MadsRudolph/34621-Metal-Detector/Literature/20240103_144208.jpg

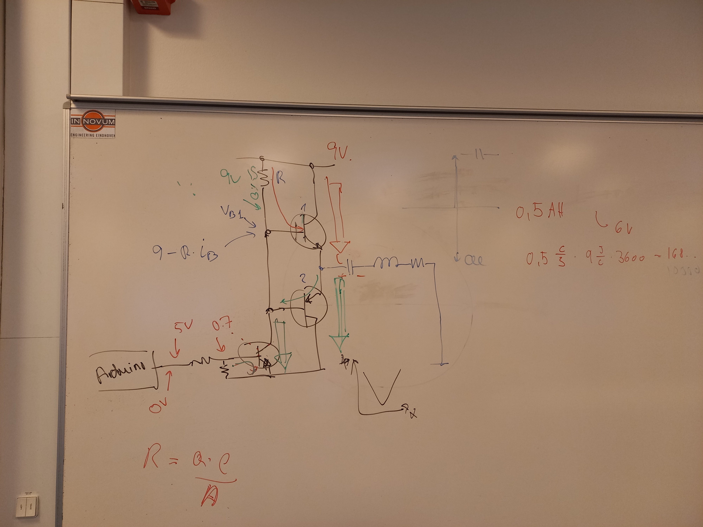
Literature/20240103_144208.jpg
