MadsRudolph/34621-Metal-Detector/Docs/Templates/Circuit Note.md

# {{Circuit Name}}

**Type:** (Amplifier / Filter / Driver / Power Supply)  
**Status:** ⬜ Design | ⬜ Simulated | ⬜ Built | ⬜ Tested

---

## Purpose

## Schematic

![[{{schematic_image}}]]

## Component Values

| Component | Value | Part Number | Notes |
|---|---|---|---|
| R1 | | | |
| C1 | | | |
| U1 | | | |

## Design Calculations

### Input Parameters
- 

### Calculations
$$

$$

### Expected Output
- 

## Simulation Results

**LTspice File:** [[LTspice/simulations/{{filename}}.asc]]

### Transient Analysis

### AC Analysis (Bode Plot)

## Test Results

| Parameter | Expected | Measured | Pass? |
|---|---|---|---|
| | | | |

## Issues & Solutions

## Related
- [[KiCad/README|KiCad Schematic]]
- [[LTspice/README|LTspice Simulation]]

---
#circuit #analog
