MadsRudolph/34621-Metal-Detector/Docs/Meetings/Referat af møde 8-1-2026.md

Vi har lavet et spole design tunening kan forekomme
Vi har gennemført simulering af forskellige varianter af spole dimensioner
Softwaren for TX, RX og DSP delen er ved at være nået til et punkt hvor det kan testes
Vi har lavet en fungerende Hbro forstærker til A.P forstærkeren, der er enkelte problemer bla at PMOS'erne i kredsløbet måske ville ryge ud af saturation lidt efter lidt som batteriet taber spænding.
Vi har sat os fast på en spole ydre diameter på 20cm så vi kan gå i gang med at lave en 3D model af metaldetektoren.
Vi ville gerne have en prototype udgave af softwaren både til DSP, Tx, Rx og A.P styring klar til slutningen af den 9-1-2026.
Til uge 3 skal alt være klar til test så vi kan udnytte ugen til test og redesign.
Rx forstærkeren skal have et færdigt grunddesign til begyndelsen af uge 3, så vi kan teste justeringer kan forekomme.
Vi ville gerne så småt begynde at skrive vores sota og analyse ind i raporten fra idag af.
