MadsRudolph/34621-Metal-Detector/Docs/Templates/Daily Note.md

# {{date:YYYY-MM-DD}} - Daily Log

## 🎯 Goals for Today
- [ ] 
- [ ] 
- [ ] 

## ✅ Completed
- 

## 📝 Notes

## ❓ Questions
- 

## 🐛 Issues Encountered

## 📅 Tomorrow
- 

---
#daily
