MadsRudolph/34621-Metal-Detector/Docs/Templates/Literature Note.md

# {{title}}

**Source:** [[Literature/{{filename}}]]  
**Date Read:** {{date}}  
**Relevance:** ⭐⭐⭐⭐⭐

---

## Summary

## Key Concepts

### Concept 1

### Concept 2

## Important Equations

$$

$$

## Figures/Diagrams

## How This Applies to Our Project

## Questions

## Related Notes
- 

---
#literature #reading-notes
