MadsRudolph/34621-Metal-Detector/assets/photos/3D_modeller_samlet.png

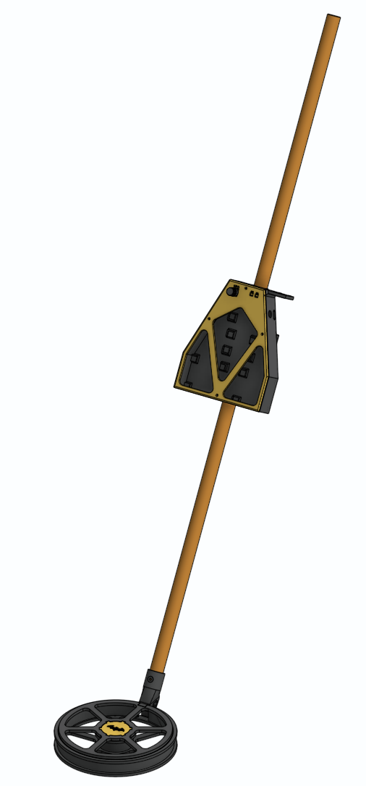
assets/photos/3D_modeller_samlet.png
