MadsRudolph/34621-Metal-Detector/assets/photos/Dead_Time_forklarings_diagram.png

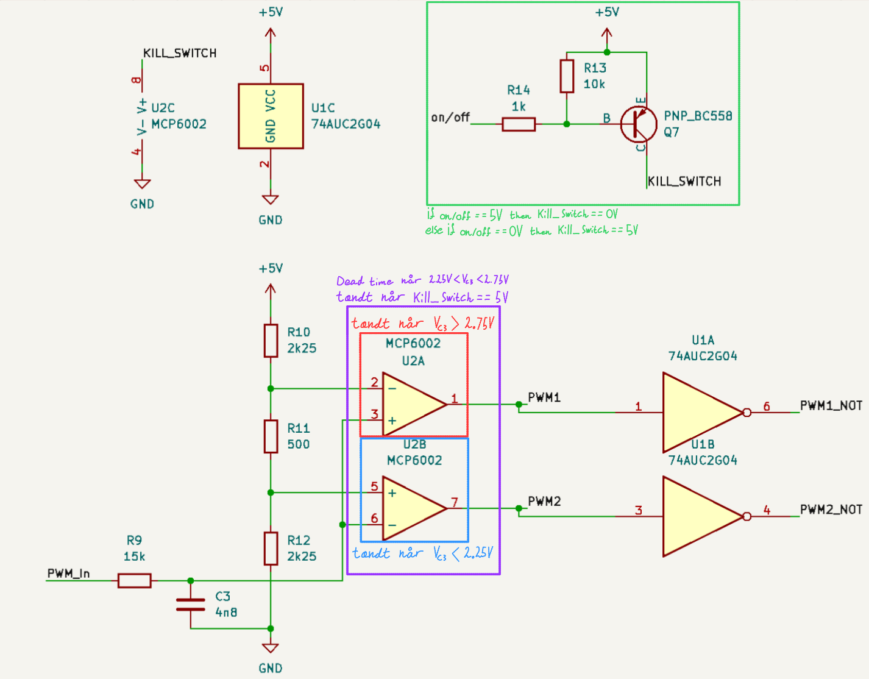
assets/photos/Dead_Time_forklarings_diagram.png
