MadsRudolph/34621-Metal-Detector/assets/photos/Dead_Time_PCB.png

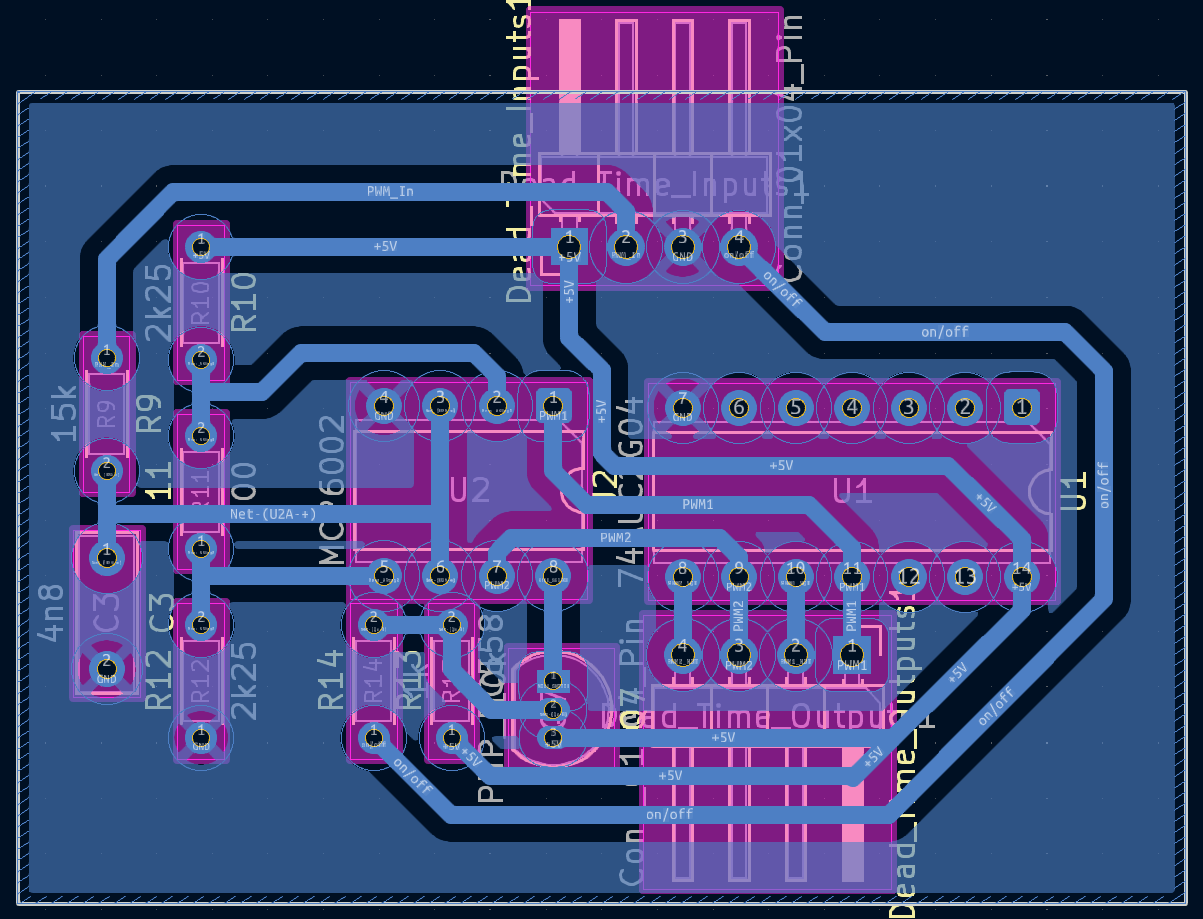
assets/photos/Dead_Time_PCB.png
