MadsRudolph/34621-Metal-Detector/assets/photos/Højre_PCB.png

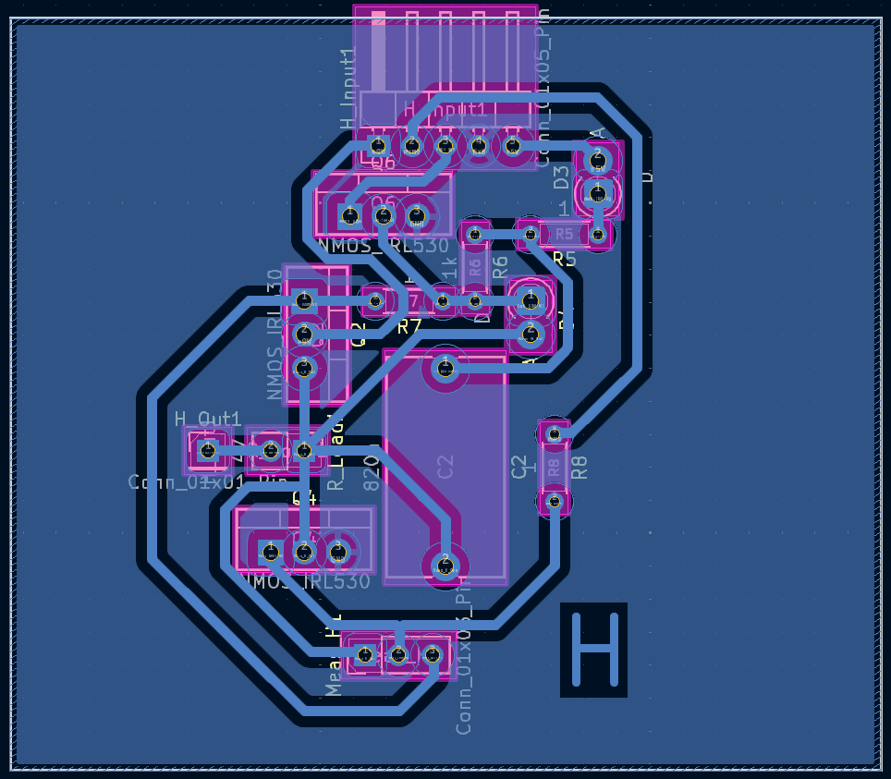
assets/photos/Højre_PCB.png
