MadsRudolph/34621-Metal-Detector/assets/photos/RX-filter_simulation.png

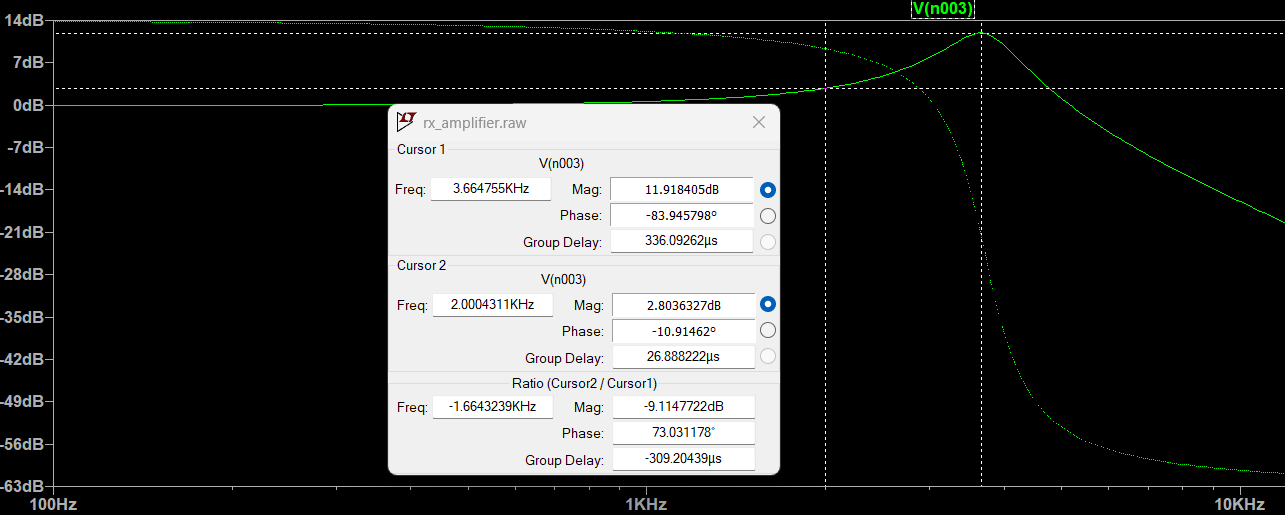
assets/photos/RX-filter_simulation.png
