MadsRudolph/34621-Metal-Detector/assets/photos/Rx_amp.png

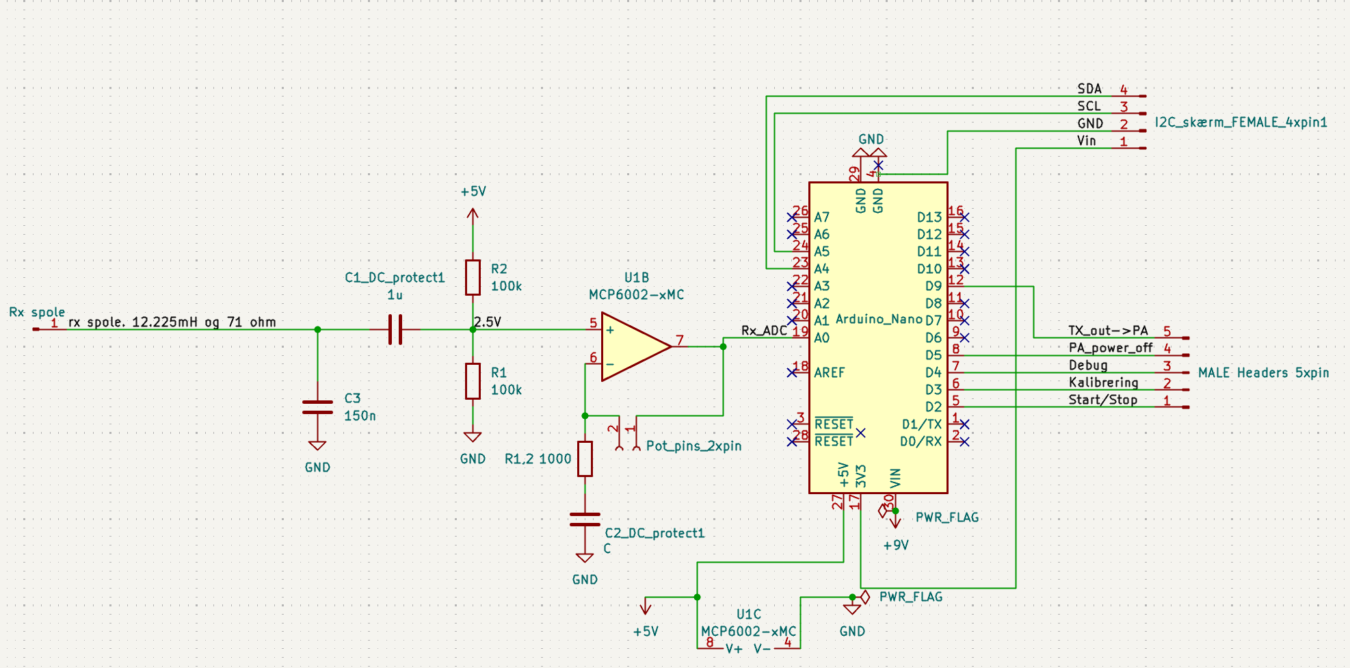
assets/photos/Rx_amp.png
