MadsRudolph/34621-Metal-Detector/assets/photos/Rx_forstærker_PCB.png

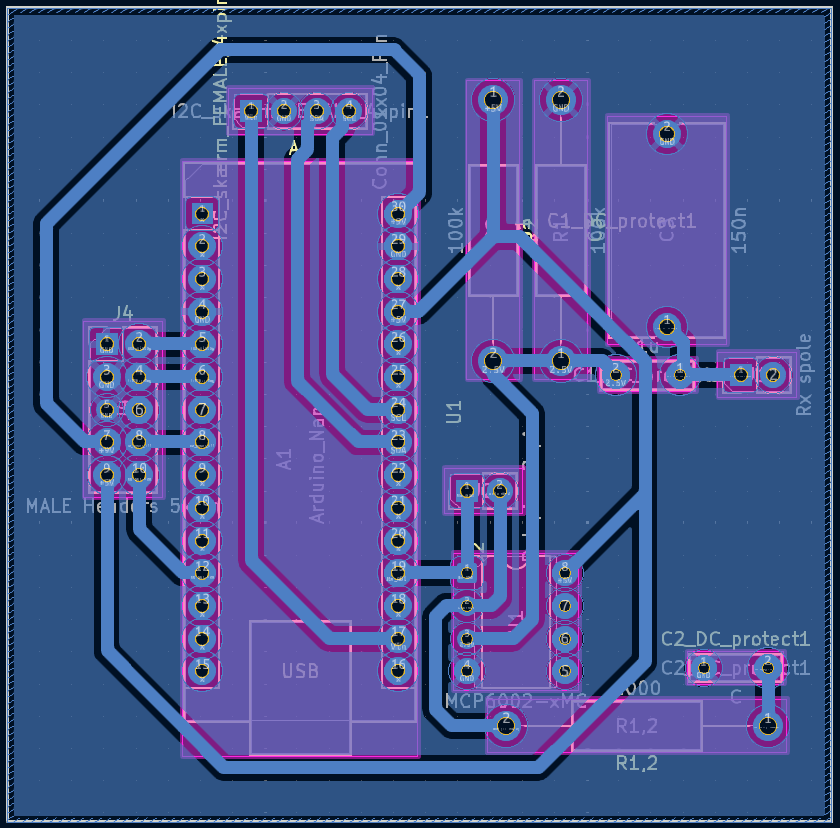
assets/photos/Rx_forstærker_PCB.png
