MadsRudolph/34621-Metal-Detector/assets/photos/Simulering_Hbro.png

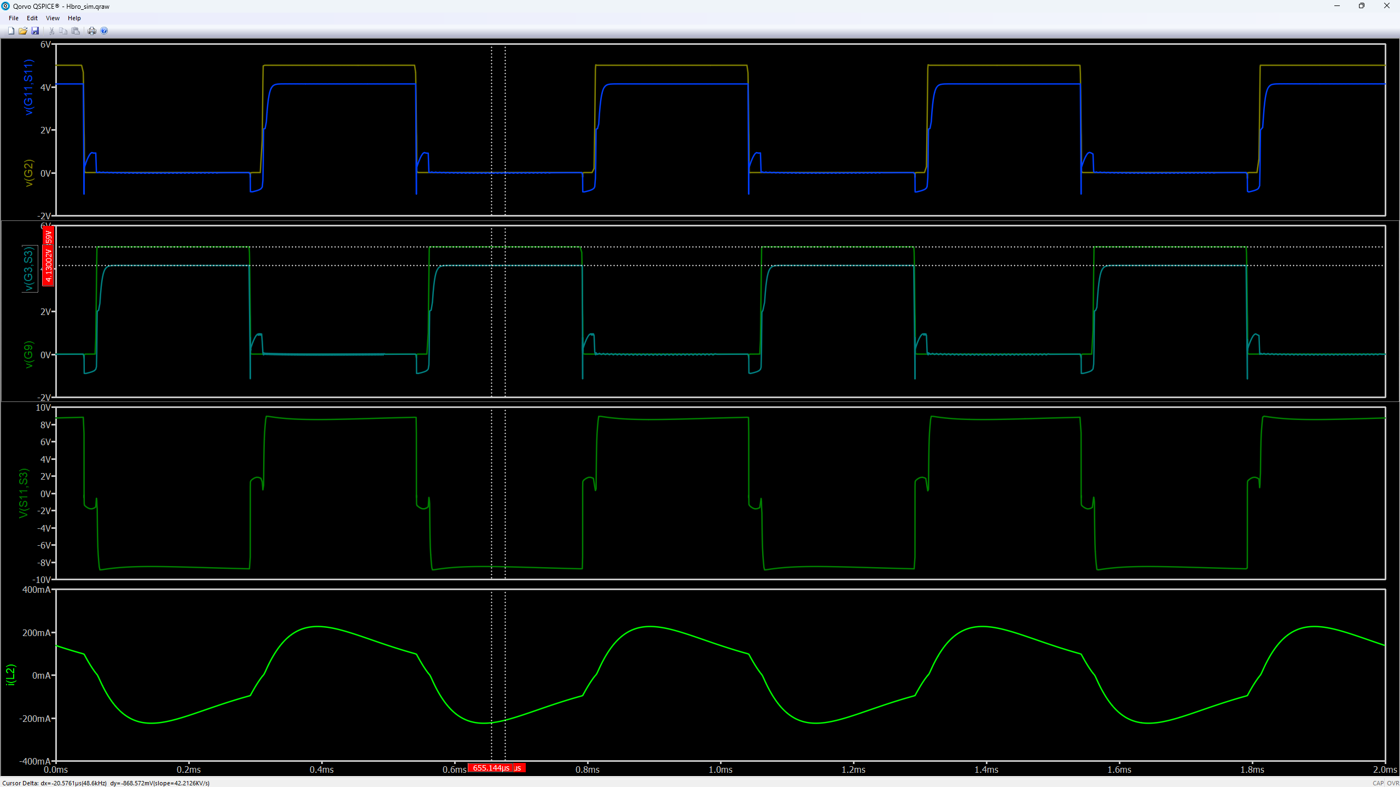
assets/photos/Simulering_Hbro.png
