MadsRudolph/34621-Metal-Detector/assets/photos/Timer1.png

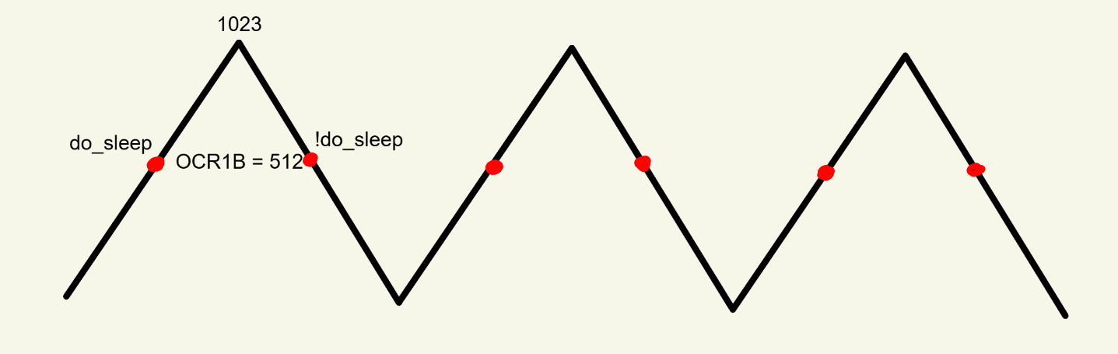
assets/photos/Timer1.png
