MadsRudolph/34621-Metal-Detector/Docs/Images/Deadtime_Blue-PWM1_not_Yellow-PWM1___5_us.png

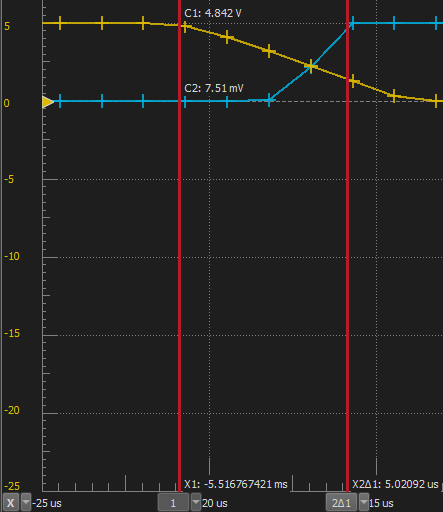
Docs/Images/Deadtime_Blue-PWM1_not_Yellow-PWM1___5_us.png
