MadsRudolph/34621-Metal-Detector/Docs/Images/dft_samples.png

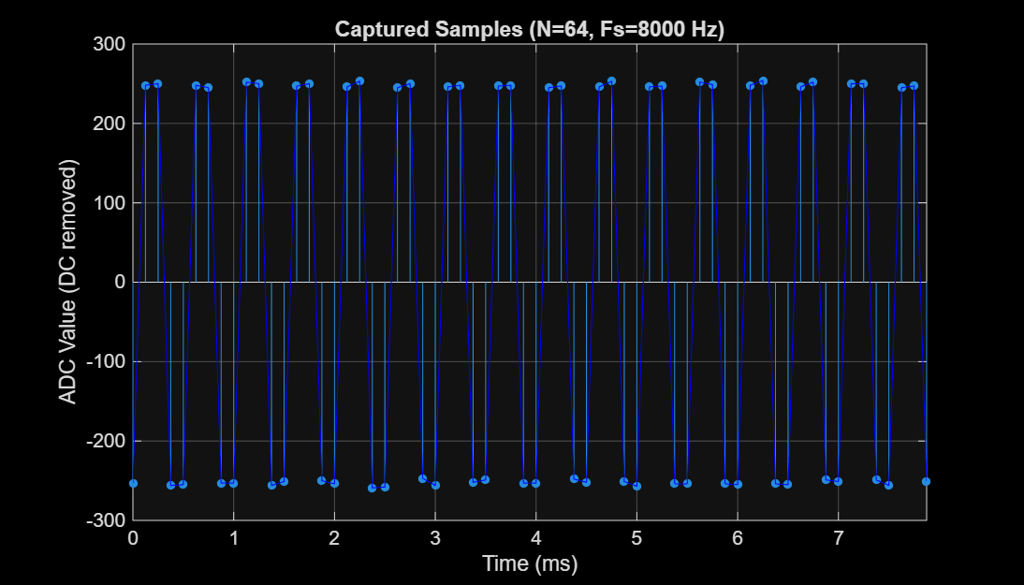
Docs/Images/dft_samples.png
