MadsRudolph/34621-Metal-Detector/Docs/Images/Differential_output.png

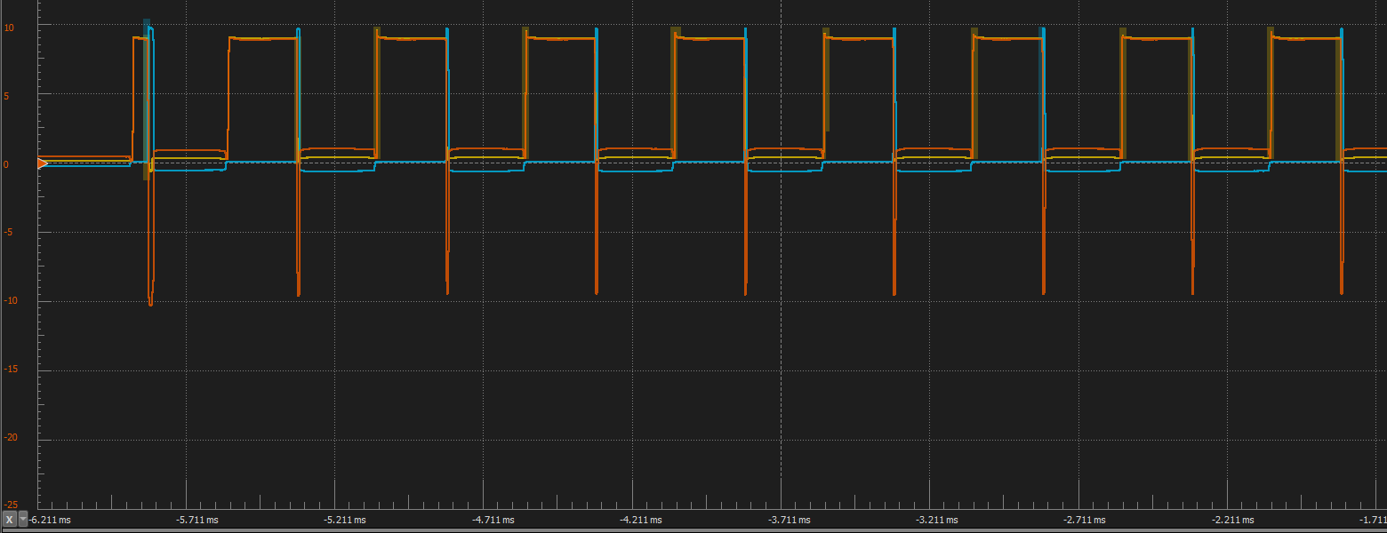
Docs/Images/Differential_output.png
