MadsRudolph/34621-Metal-Detector/Docs/Images/Gate_drive_signal_left_Yellow-Highside_Blue-lowside.png

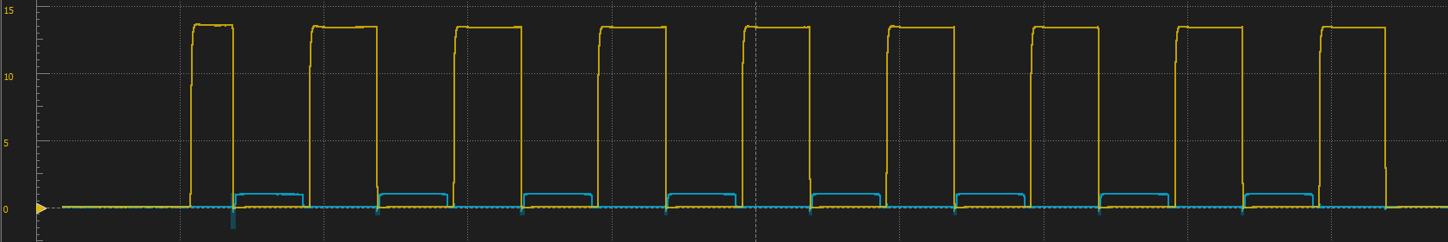
Docs/Images/Gate_drive_signal_left_Yellow-Highside_Blue-lowside.png
