MadsRudolph/34621-Metal-Detector/Docs/Images/Gates/gatem4_yellow-højre_blue-left.png

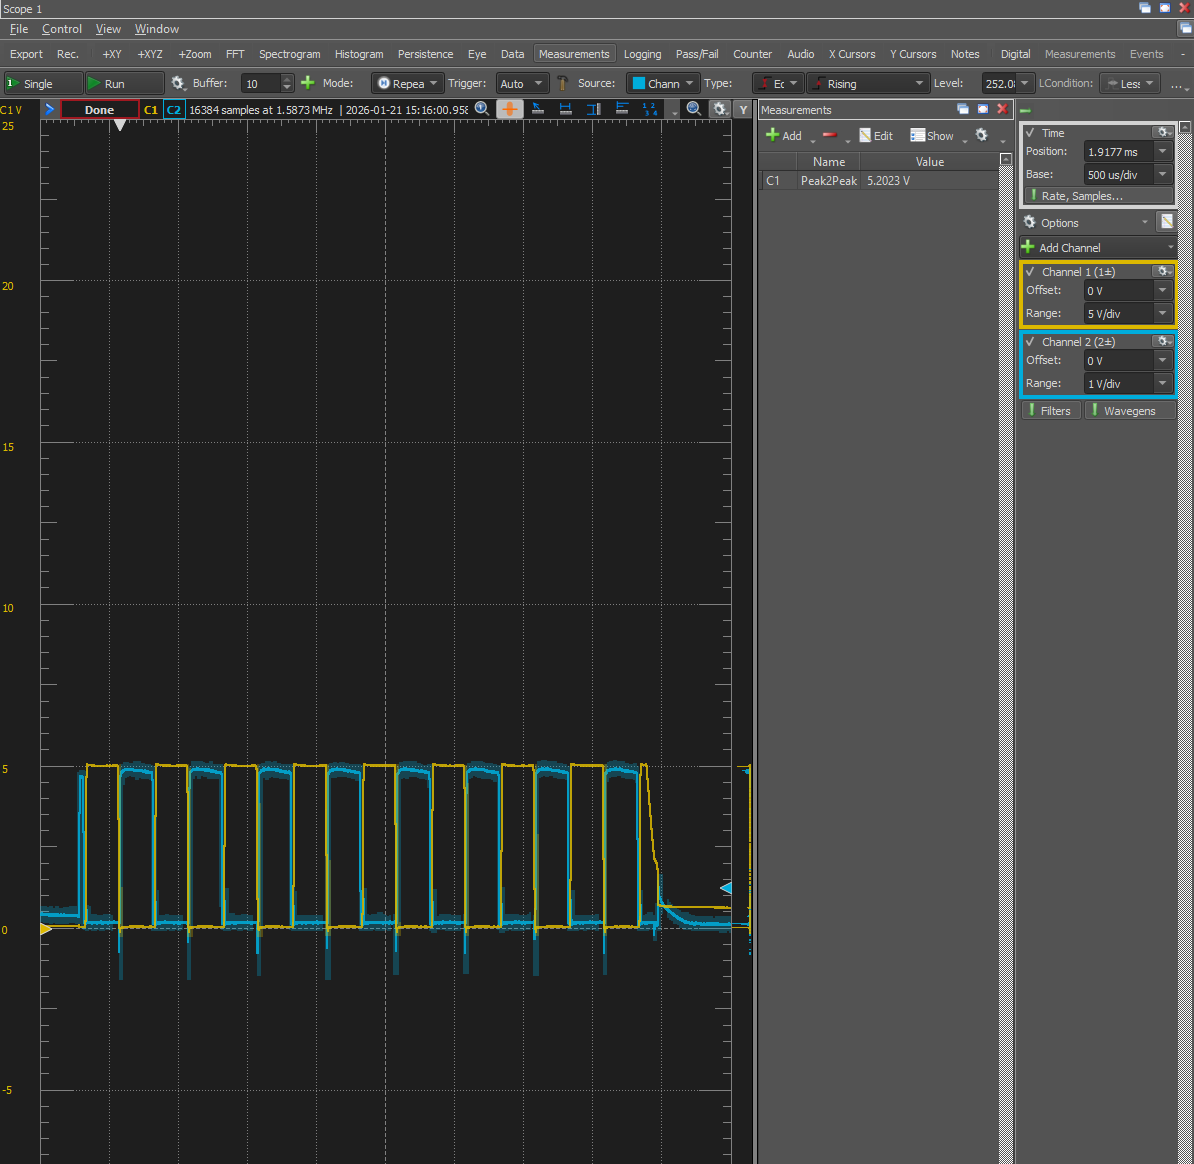
Docs/Images/Gates/gatem4_yellow-højre_blue-left.png
