MadsRudolph/34621-Metal-Detector/Docs/Images/Gates/gatem4_yellow-højre_blue-left_closeup.png

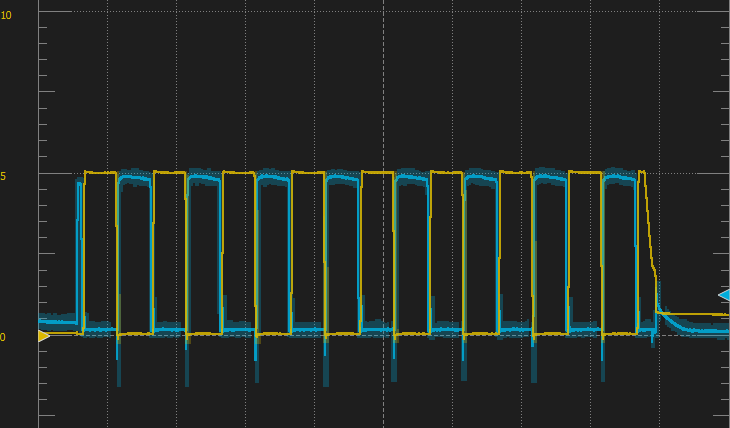
Docs/Images/Gates/gatem4_yellow-højre_blue-left_closeup.png
