MadsRudolph/34621-Metal-Detector/Docs/Images/nano_vs_mega.png

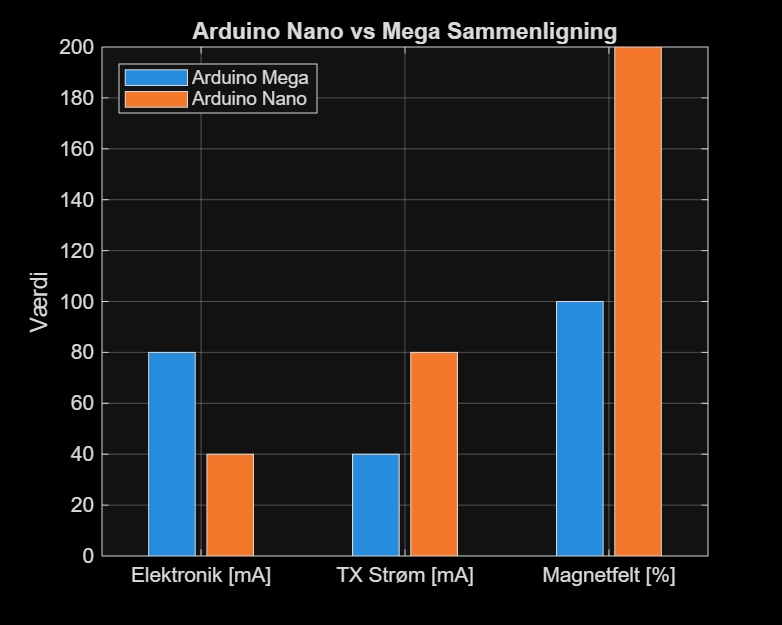
Docs/Images/nano_vs_mega.png
