MadsRudolph/34621-Metal-Detector/Docs/Images/tx_turns_vs_inductance.png

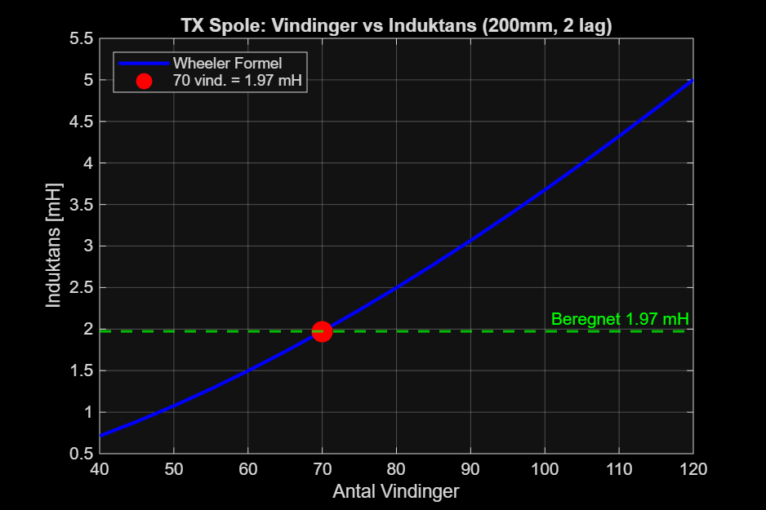
Docs/Images/tx_turns_vs_inductance.png
