MadsRudolph/34621-Metal-Detector/assets/photos/battery_discharge_test.png

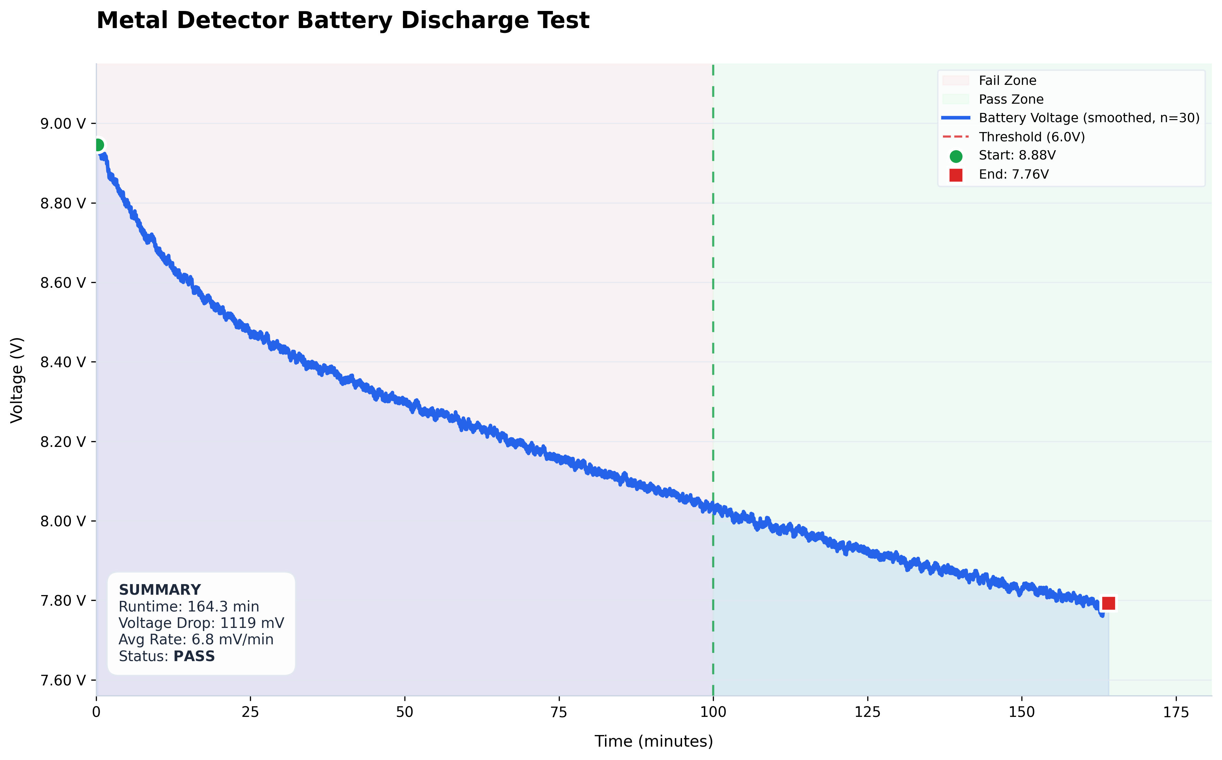
assets/photos/battery_discharge_test.png
