MadsRudolph/34621-Metal-Detector/Docs/Matlab/dft_verification.png

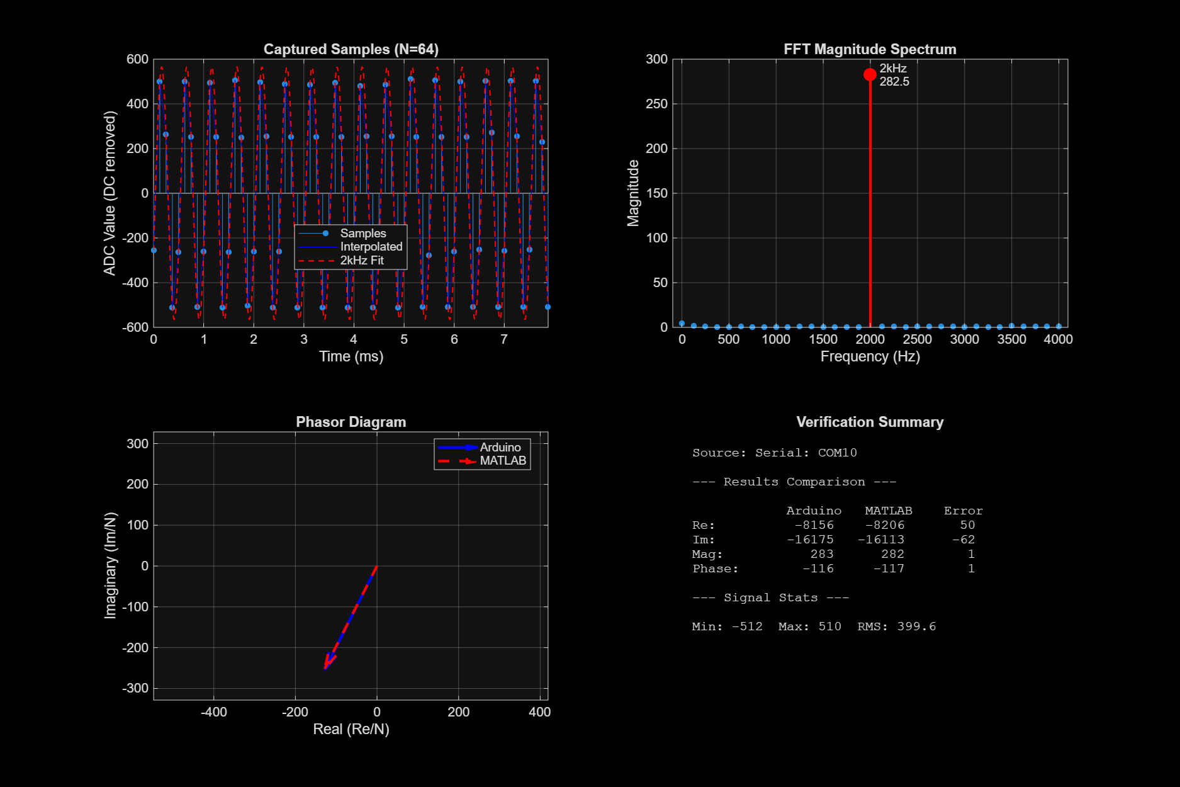
Docs/Matlab/dft_verification.png
