MadsRudolph/34621-Metal-Detector/LTspice/rx_amplifier.asc

C1: cap; 1µ
C2: cap; 1µ
C3: cap; 150n
L_rx_spole: ind; 12.255m
R1: res; 100k
R2: res; 100k
R3: res; 90k
R4: res; 14k
R_spole: res; 71
U1: UniversalOpAmp; Avol=1Meg GBW=1Meg Vos=0; En=0 Enk=0 In=0 Ink=0 Rin=1Meg
V1: voltage; 5
V2: voltage; SINE(0 200m 2k); AC 1
Named nets: 0
2.5V
.ac dec 100 1 1G
;.tran 50m
spole og modstand er en model af Rx spolens modstand og selvinduktans
