MadsRudolph/34621-Metal-Detector/LTspice/example.asc

C1: cap; 3µ
L1: ind; 0.00227
Q1: npn; BC337-25
Q2: npn; BC817-25
Q3: pnp; BC327-25
R1: res; 13.8
R2: res; 1k
R3: res; 10k
R4: res; 10k
V1: voltage; 9; Rser=1
V2: voltage; PULSE(0 5 0 1u 1u 0.25m 0.5m)
Named nets: 0
.tran 10ms
