MadsRudolph/34621-Metal-Detector/Code/src/drivers/data.h

/**
 * data.h
 * Font data for SSD1306 OLED display
 *
 * This file contains all the static arrays to draw things in the display.
 * You can create your own fonts using this tool: https://www.mikroe.com/glcd-font-creator
 *
 * ATTRIBUTION:
 * ============
 * Part of the SSD1306 driver by osch
 *
 * Integration: Mads Rudolph, Andreas Skaaning, Jonas Beck & Sigurd Hestbech (DTU 34621 Metal Detector Project)
 */

#ifndef DATA_H_
#define DATA_H_

#include <avr/pgmspace.h>
#include <stdint.h>

typedef uint8_t bitmap_t[8][128];
typedef char PROGMEM prog_uchar;

// Big numbers font, from 0 to 9. 96 byte each.
const prog_uchar bigNumbers [][96] PROGMEM = {
{0x00, 0x00, 0x00, 0xC0, 0xE0, 0xF0, 0xF0, 0xF0, 0xF0, 0xF0, 0xF0, 0xF0, 0xF0, 0xF0, 0xF0, 0xF0,
0xF0, 0xF0, 0xF0, 0xE0, 0xC0, 0x00, 0x00, 0x00, 0x00, 0x00, 0x00, 0xFF, 0xFF, 0xFF, 0xFF, 0x01,
0x00, 0x00, 0x00, 0x00, 0x00, 0x00, 0x00, 0x00, 0x01, 0xFF, 0xFF, 0xFF, 0xFF, 0x00, 0x00, 0x00,
0x00, 0x00, 0x00, 0xFF, 0xFF, 0xFF, 0xFF, 0x80, 0x00, 0x00, 0x00, 0x00, 0x00, 0x00, 0x00, 0x00,
0x80, 0xFF, 0xFF, 0xFF, 0xFF, 0x00, 0x00, 0x00, 0x00, 0x00, 0x00, 0x03, 0x07, 0x0F, 0x0F, 0x0F,
0x0F, 0x0F, 0x0F, 0x0F, 0x0F, 0x0F, 0x0F, 0x0F, 0x0F, 0x0F, 0x0F, 0x07, 0x03, 0x00, 0x00, 0x00},

{0x00, 0x00, 0x00, 0x00, 0x00, 0x00, 0x00, 0x00, 0x00, 0x00, 0x00, 0x00, 0x00, 0x00, 0xE0, 0xF0,
0xF0, 0xE0, 0x00, 0x00, 0x00, 0x00, 0x00, 0x00, 0x00, 0x00, 0x00, 0x00, 0x00, 0x00, 0x00, 0x00,
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
const prog_uchar bar_low[8] PROGMEM =   {0x00,0x7E,0x42,0x5A,0x5A,0x42,0x7E,0x00};
const prog_uchar bar_med[8] PROGMEM =   {0x00,0x7E,0x5A,0x5A,0x5A,0x5A,0x7E,0x00};
const prog_uchar bar_full[8] PROGMEM =  {0x00,0x7E,0x7E,0x7E,0x7E,0x7E,0x7E,0x00};

#endif // DATA_H_
